Jaquetaa/Ember/assets/comando/ember comando.png

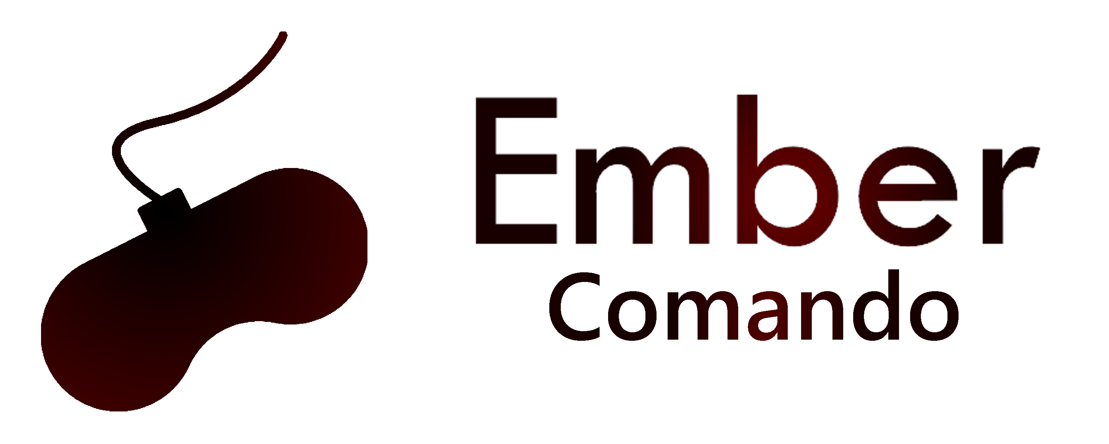
assets/comando/ember comando.png
