Jaquetaa/Ember/assets/diagrama/arrows playground.png

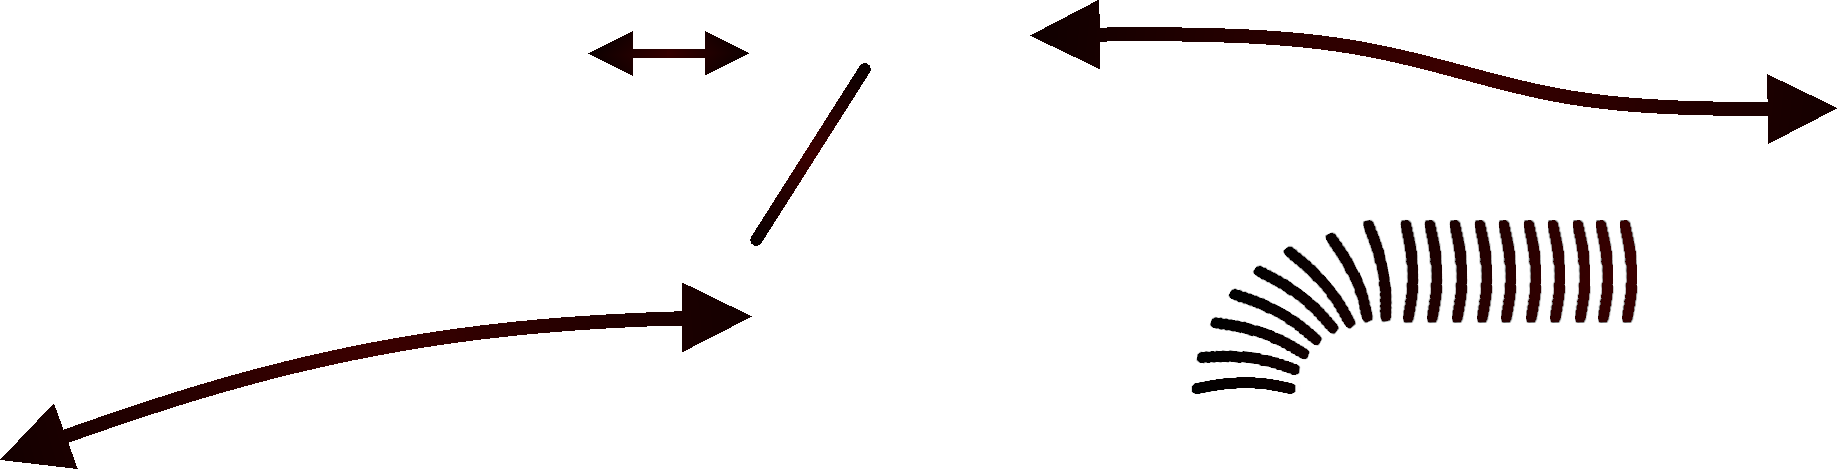
assets/diagrama/arrows playground.png
