Jaquetaa/Ember/assets/diagrama/cam.png

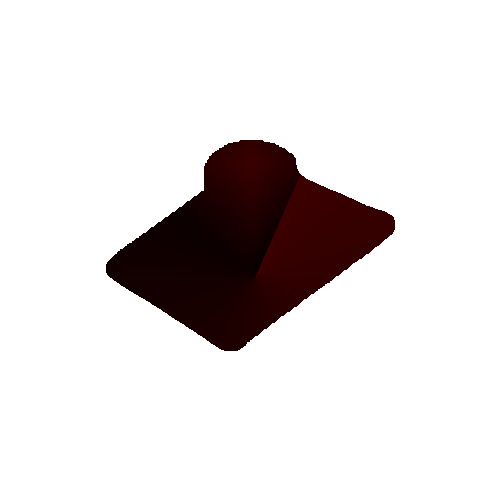
assets/diagrama/cam.png
