Jaquetaa/Ember/assets/diagrama/chama.png

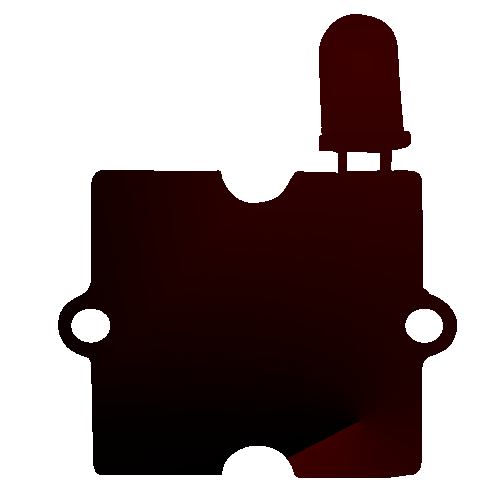
assets/diagrama/chama.png
