Jaquetaa/Ember/assets/diagrama/ember drone.png

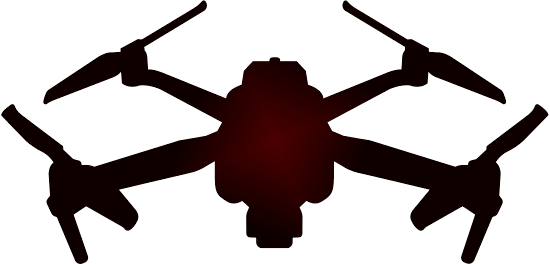
assets/diagrama/ember drone.png
