Jaquetaa/Ember/assets/diagrama/esp32s3.png

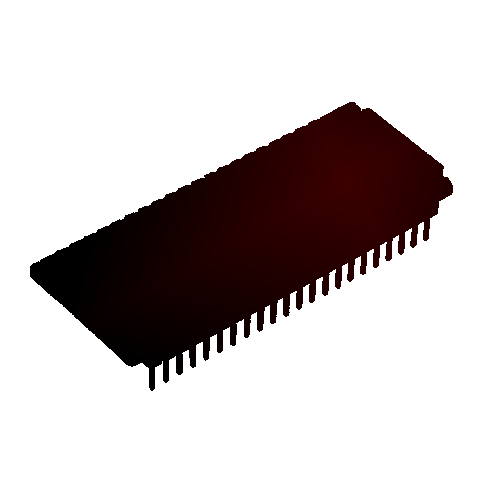
assets/diagrama/esp32s3.png
