Jaquetaa/Ember/assets/diagrama/gás.png

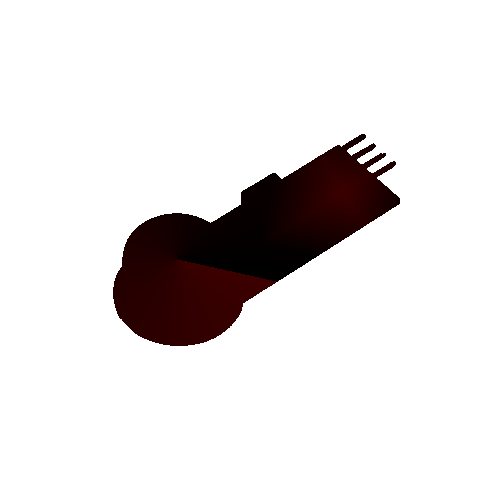
assets/diagrama/gás.png
