Jaquetaa/Ember/assets/diagrama/joystick.png

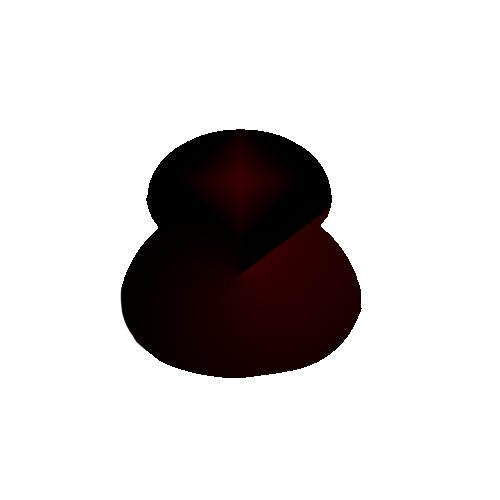
assets/diagrama/joystick.png
