Jaquetaa/Ember/assets/diagrama/radio waves.png

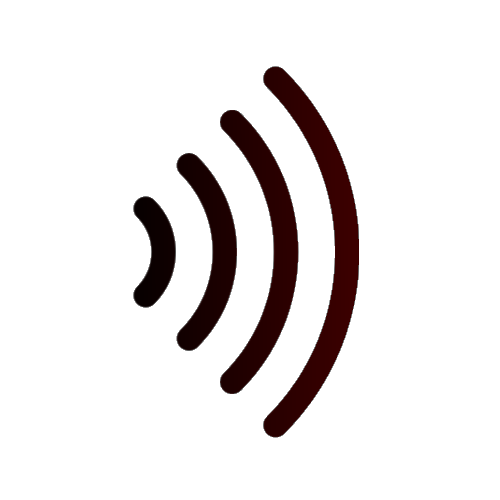
assets/diagrama/radio waves.png
