Jaquetaa/Ember/assets/diagrama/tactile push button.png

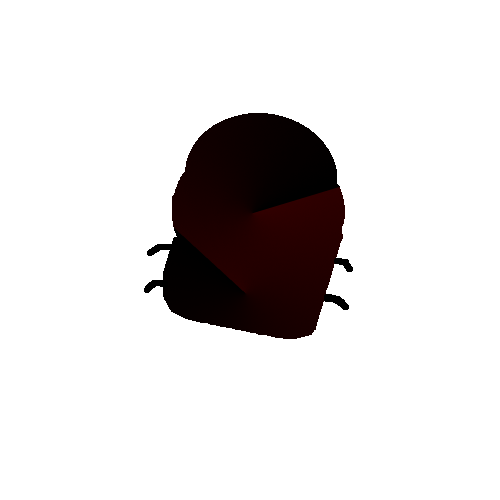
assets/diagrama/tactile push button.png
