Jaquetaa/Ember/assets/ember cycle.gif

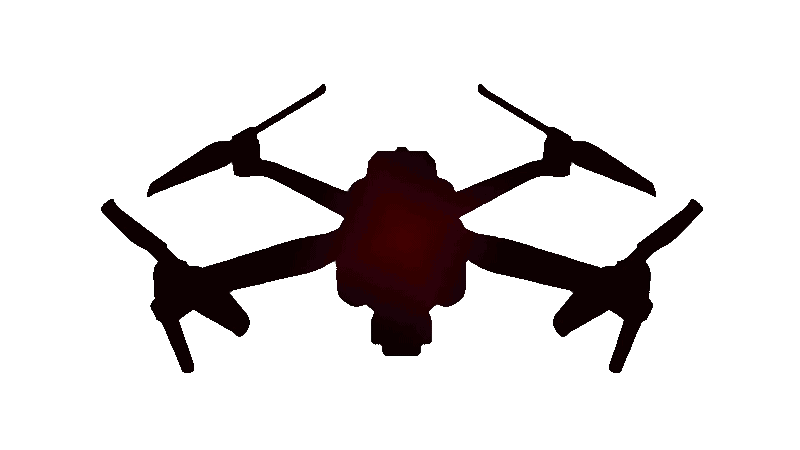
assets/ember cycle.gif
