Jaquetaa/Ember/assets/empresas-big-love/aralab.png

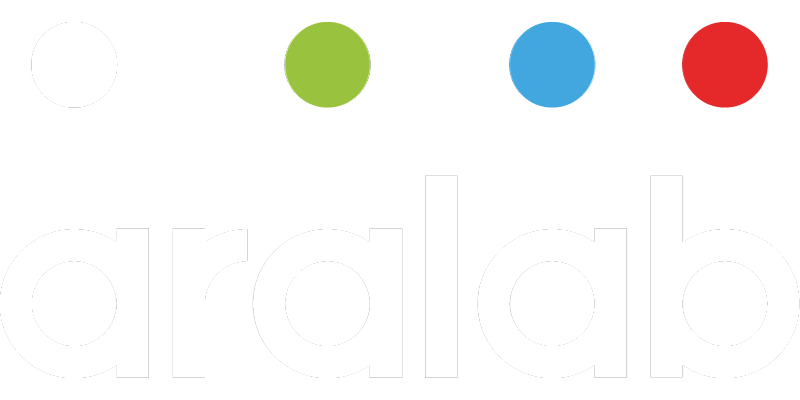
assets/empresas-big-love/aralab.png
