Jaquetaa/Ember/assets/empresas-big-love/tekever.png

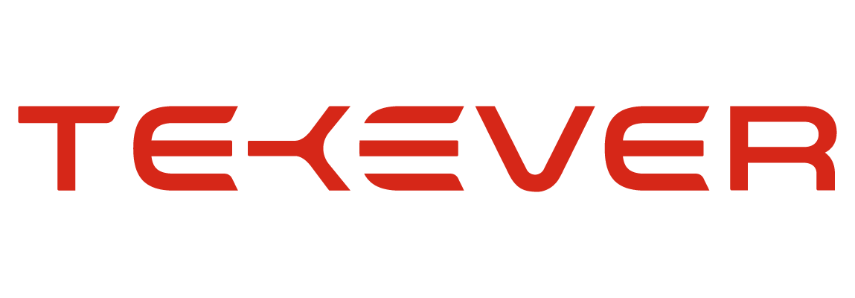
assets/empresas-big-love/tekever.png
