Jaquetaa/Ember/assets/other/edu2024-black.png

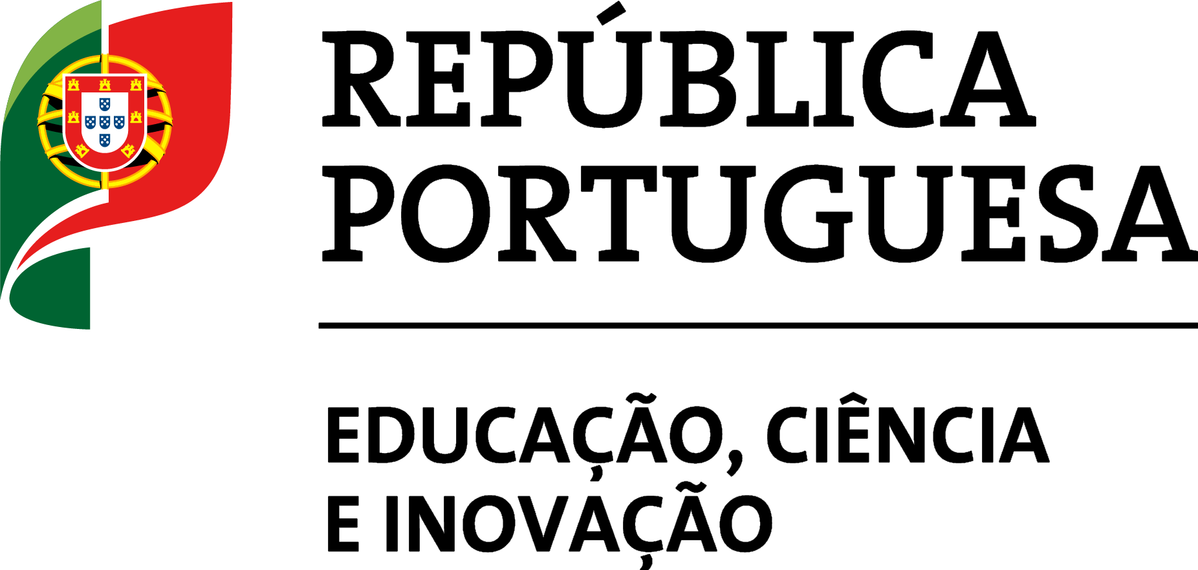
assets/other/edu2024-black.png
