Jaquetaa/Ember/assets/other/edu2024-white.png

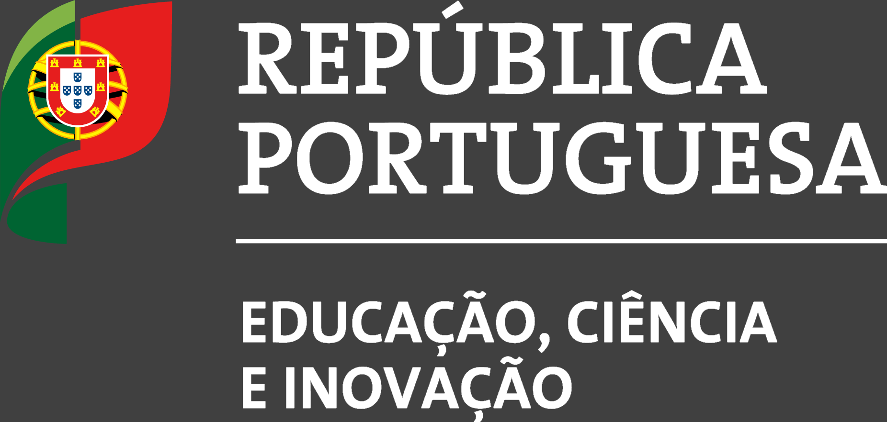
assets/other/edu2024-white.png
