Jaquetaa/Ember/assets/other/warning.png

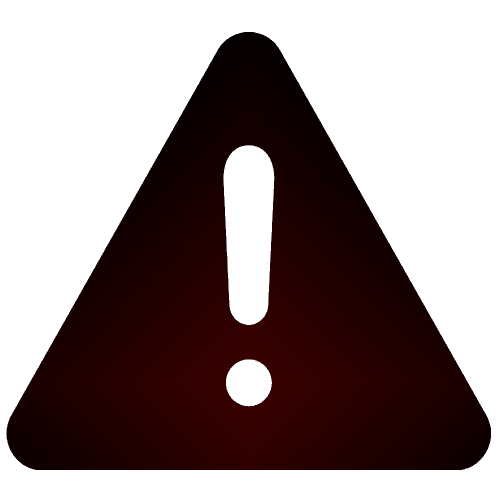
assets/other/warning.png
